alfredtorch/RGBFighter/images/WidgetEsp8266RGBv4StripBottom.png

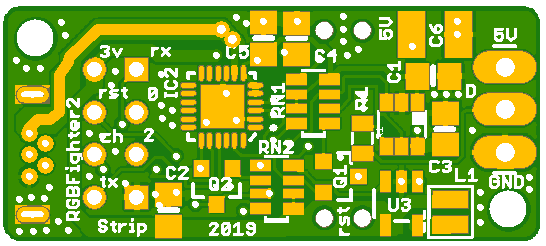
images/WidgetEsp8266RGBv4StripBottom.png
